wblachowski/soil-moisture-monitor/main/ButtonHandler.cpp

#include "ButtonHandler.h"

ButtonHandler::ButtonHandler(int dbncTime)
{
    lastState = 0;
    lastChange = 0L;
    debounceTime = dbncTime;
    disabled = false;
}

unsigned long ButtonHandler::pressTime(int state, unsigned long now)
{

    if (lastState != state)
    {
        lastState = state;
        lastChange = now;
        disabled = false;
    }

    if (disabled)
    {
        return 0L;
    }

    if (state && state == lastState && (now - lastChange) > debounceTime)
    {
        return now - lastChange;
    }
    return 0L;
}

void ButtonHandler::disableUntilChange()
{
    disabled = true;
}
