wblachowski/soil-moisture-monitor/main/ButtonHandler.h

class ButtonHandler
{
public:
    ButtonHandler(int dbncTime);
    unsigned long pressTime(int state, unsigned long now);
    void disableUntilChange();

private:
    int lastState;
    unsigned long lastChange;
    int debounceTime;
    bool disabled;
};
